Egokitek/TopoTron/Prototipo/Imagenes/Topotronprototipo.png

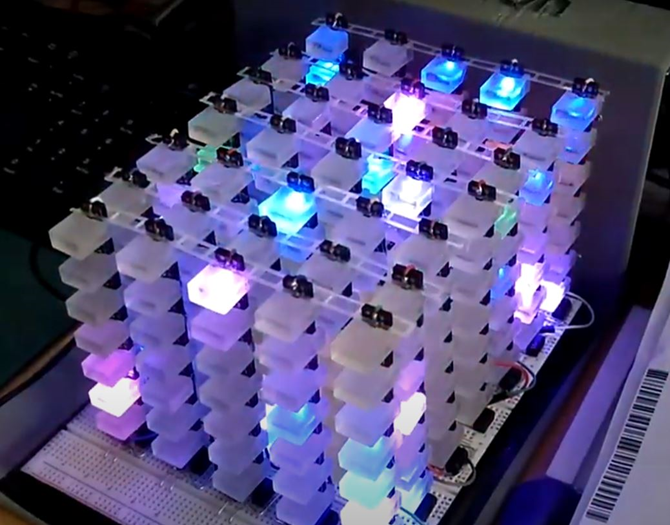
Prototipo/Imagenes/Topotronprototipo.png
