Egokitek/TopoTron/Versión de 6 módulos V2/Imagenes/Base con placas conexion.png

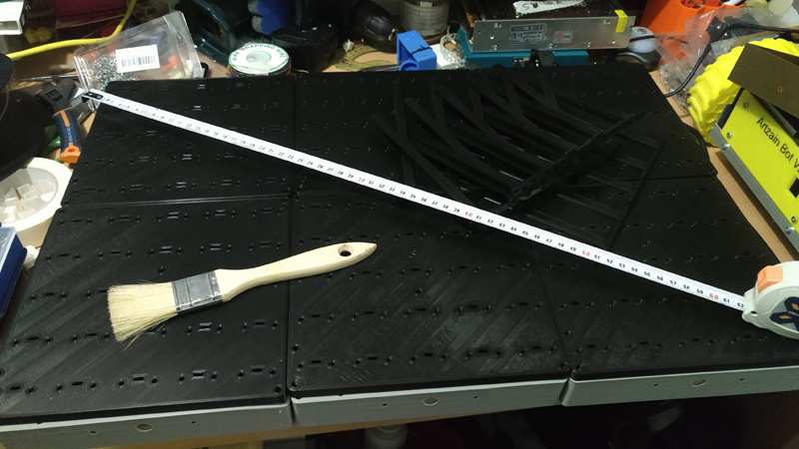
Versión de 6 módulos V2/Imagenes/Base con placas conexion.png
