Egokitek/TopoTron/Versión de 6 módulos V2/Imagenes/Base vista frontal.png

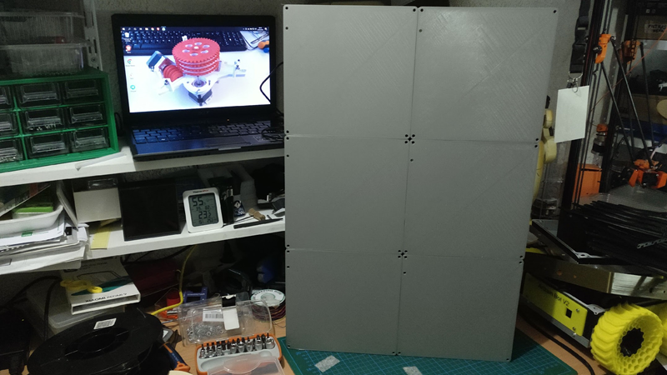
Versión de 6 módulos V2/Imagenes/Base vista frontal.png
