Egokitek/TopoTron/Versión de 6 módulos V2/Imagenes/TopotronL2.png

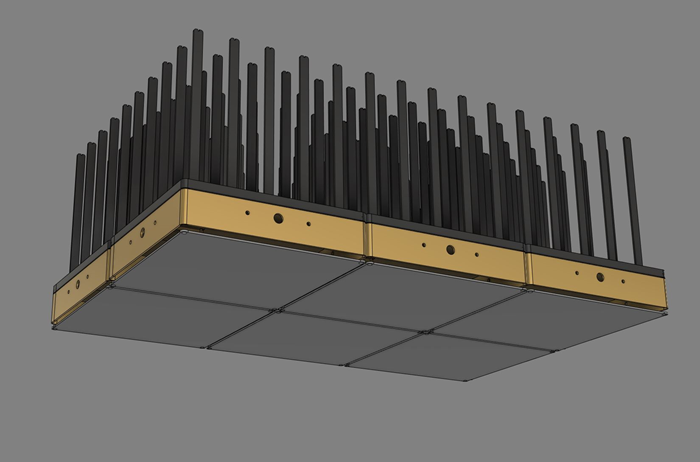
Versión de 6 módulos V2/Imagenes/TopotronL2.png
