Egokitek/TopoTron/Versión de 6 módulos V2/Imagenes/TopotronL3.png

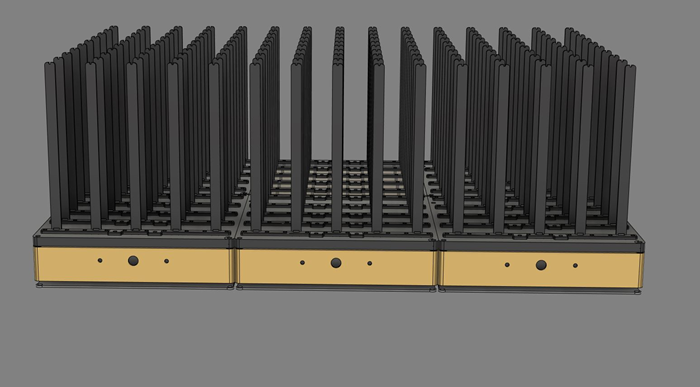
Versión de 6 módulos V2/Imagenes/TopotronL3.png
