Egokitek/TopoTron/V1/STL/Rotulo Topotron mini.stl

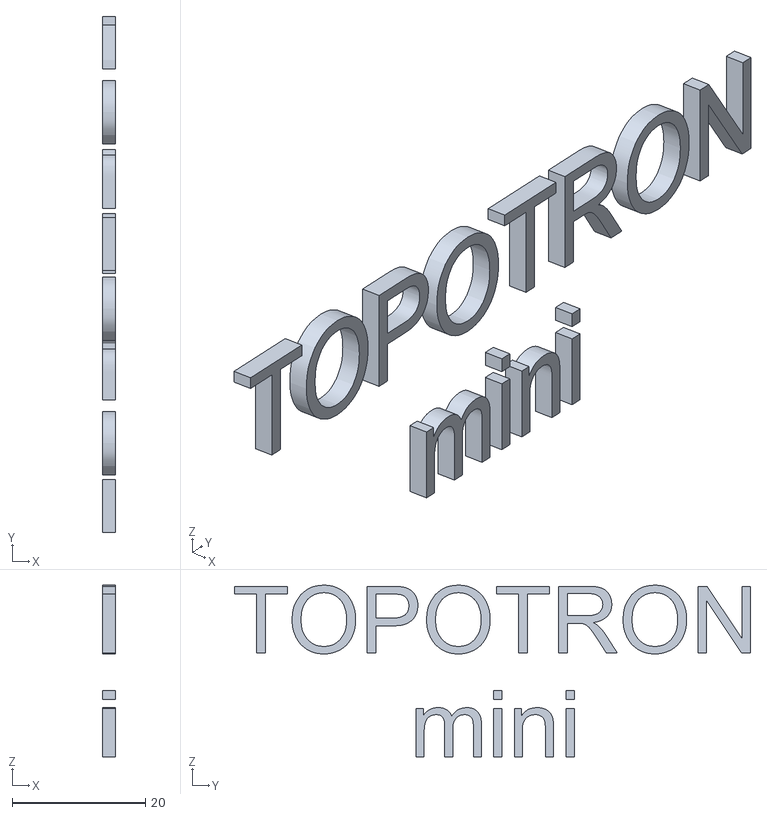
[picture p56: CAD file, 2022-09-19]
V1/STL/Rotulo Topotron mini.stl
2.00 x 77.4 x 25.8
