Egokitek/TopoTron/V2 FINAL/STL/celda CUAD v3.stl

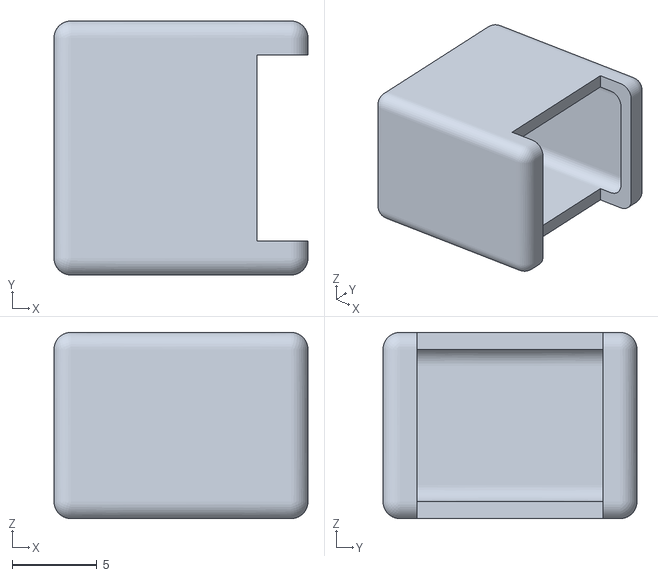
[picture p57: CAD file, 2022-09-19]
V2 FINAL/STL/celda CUAD v3.stl
15.0 x 15.0 x 11.0
