Egokitek/TopoTron/Prototipo/STL/Sop sup barras.stl

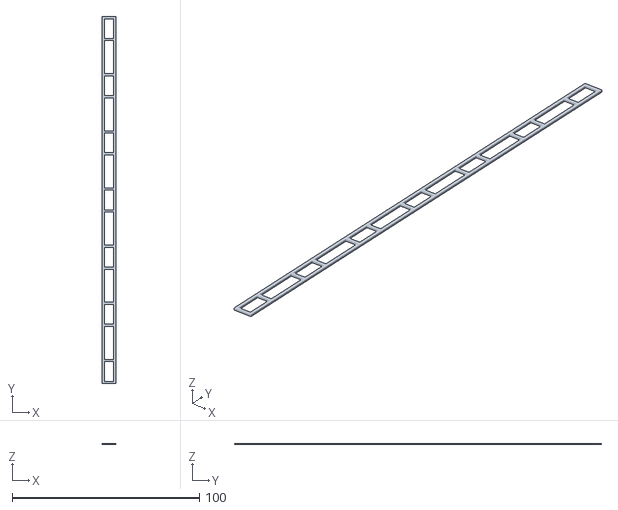
[picture p58: CAD file, 2022-09-19]
Prototipo/STL/Sop sup barras.stl
7.40 x 196.0 x 0.8
