Egokitek/TopoTron/V1/STL/Perimetro cuerpo.stl

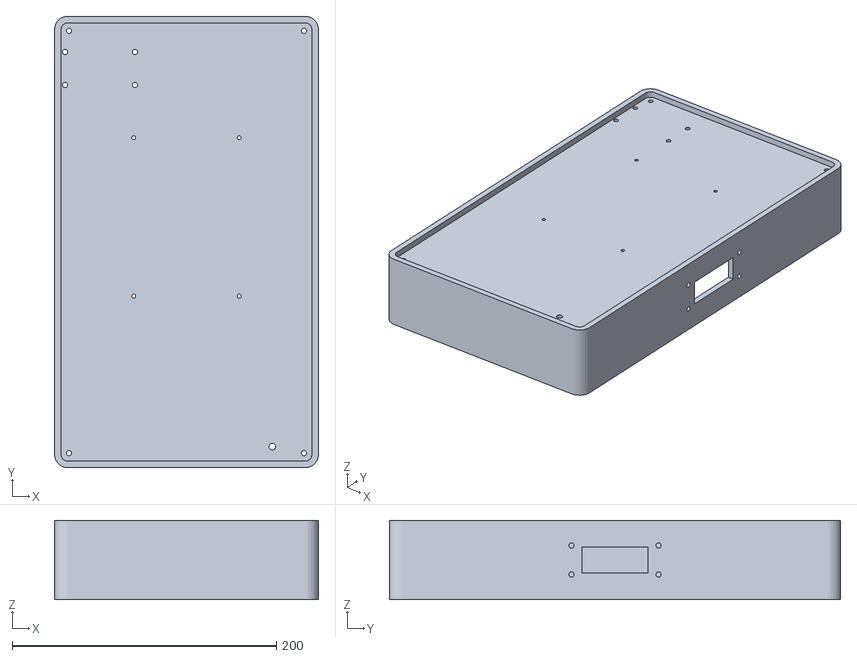
[picture p59: CAD file, 2022-09-19]
V1/STL/Perimetro cuerpo.stl
200.0 x 342.0 x 60.0
