Egokitek/TopoTron/V2 FINAL/STL/Base tiras Led 5x5.stl

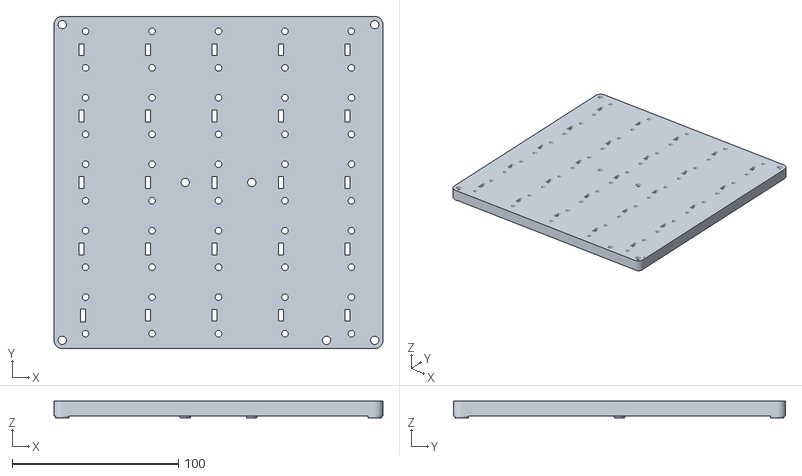
[picture p60: CAD file, 2022-09-19]
V2 FINAL/STL/Base tiras Led 5x5.stl
198.0 x 200.0 x 10.0
