Egokitek/TopoTron/V2 FINAL/STL/Barra LED 5x10.stl

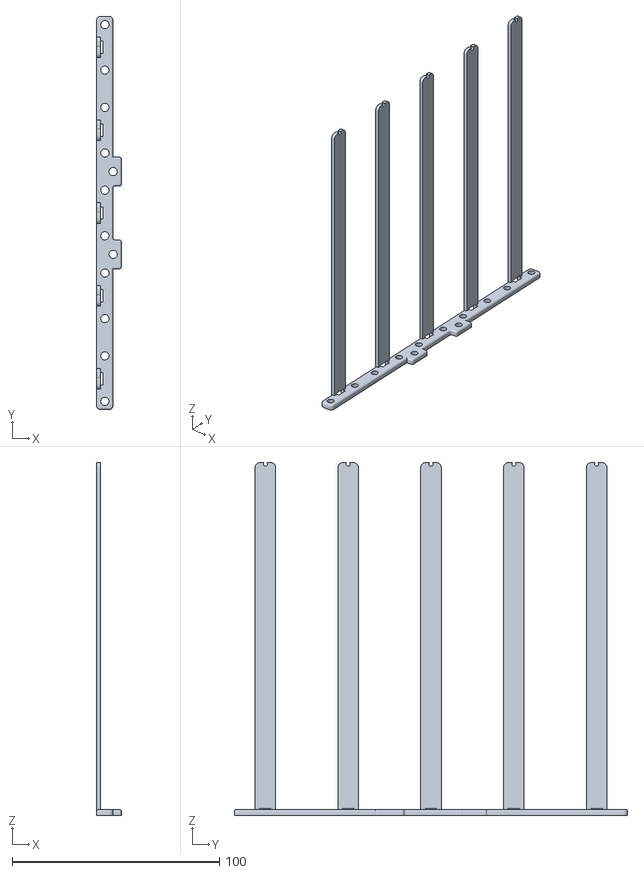
[picture p61: CAD file, 2022-09-19]
V2 FINAL/STL/Barra LED 5x10.stl
12.0 x 190.0 x 170.5
