Egokitek/TopoTron/Prototipo/STL/Celda CUADmaciza.stl

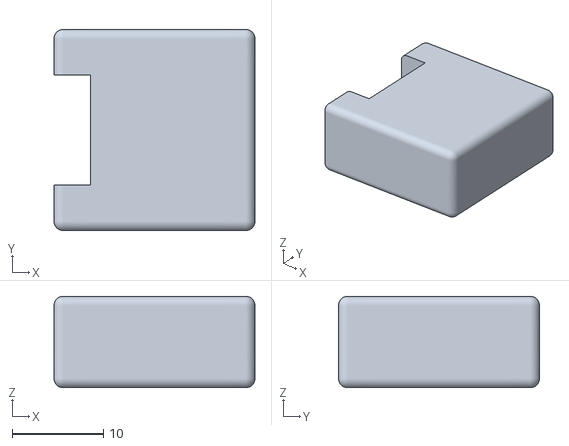
[picture p62: CAD file, 2022-09-19]
Prototipo/STL/Celda CUADmaciza.stl
22.0 x 22.0 x 10.0
