Egokitek/TopoTron/V2 FINAL/STL/Base ppal.stl

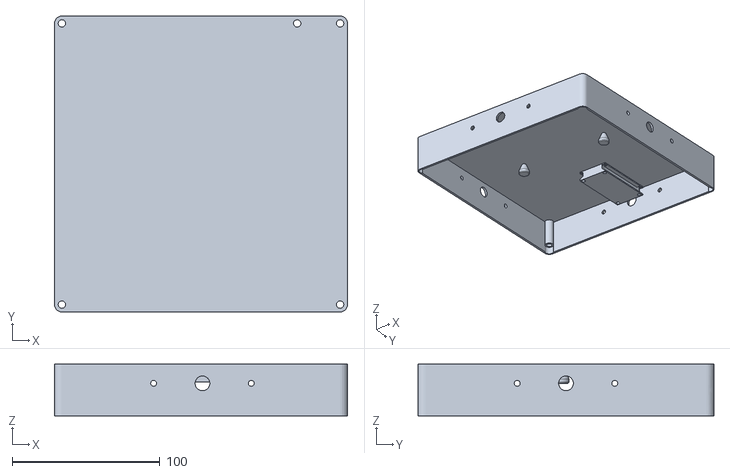
[picture p63: CAD file, 2022-09-19]
V2 FINAL/STL/Base ppal.stl
198.0 x 200.0 x 35.0
