Egokitek/TopoTron/Prototipo/STL/Celda HEX.stl

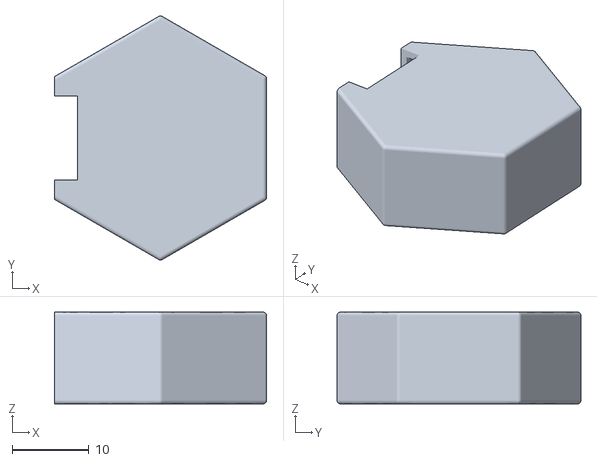
[picture p64: CAD file, 2022-09-19]
Prototipo/STL/Celda HEX.stl
27.7 x 31.8 x 12.0
